kenp-io/not-for-airpods-repairs/usb-c_protection_cases/non-pro-3_A2897_A2566/non-pro-3_A2897_A2566_HOLDER.stl

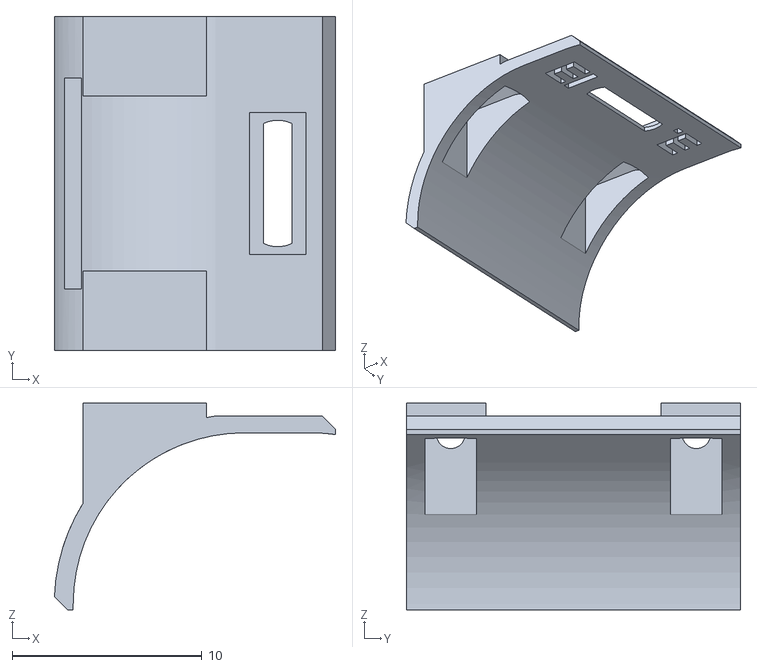
[picture p17: CAD file, 2024-10-02]
usb-c_protection_cases/non-pro-3_A2897_A2566/non-pro-3_A2897_A2566_HOLDER.stl
14.8 x 17.6 x 10.9
