kenp-io/not-for-airpods-repairs/usb-c_protection_cases/pro-1_A2190/pro-1_A2190_BOTTOM.stl

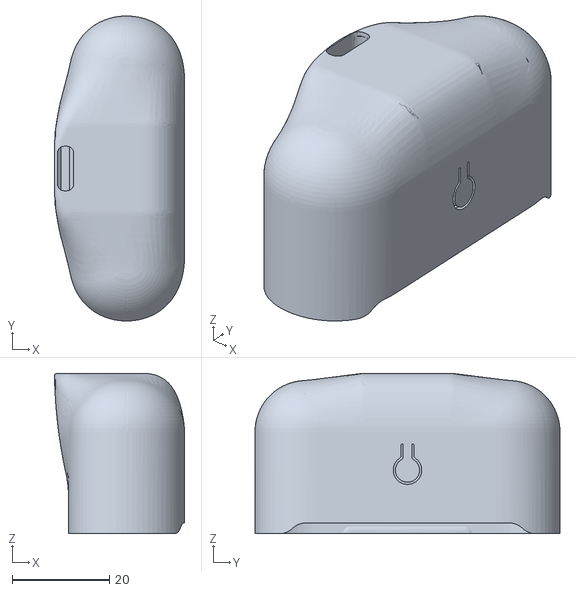
[picture p18: CAD file, 2024-10-02]
usb-c_protection_cases/pro-1_A2190/pro-1_A2190_BOTTOM.stl
26.7 x 62.6 x 32.9
